DrGlaucous/UFBTM/Media/flipped.jpg

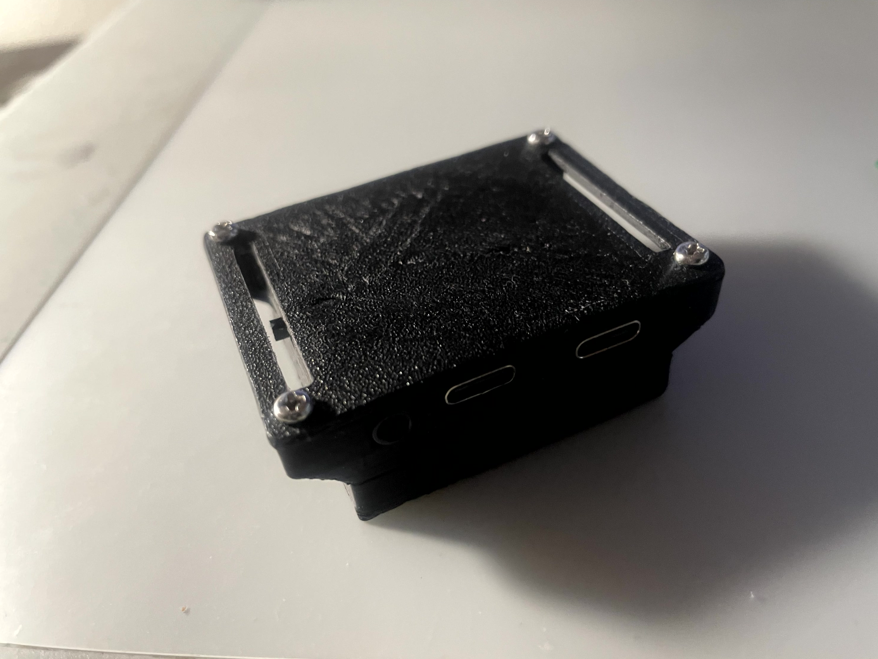
Media/flipped.jpg
