DrGlaucous/UFBTM/Media/upright.jpg

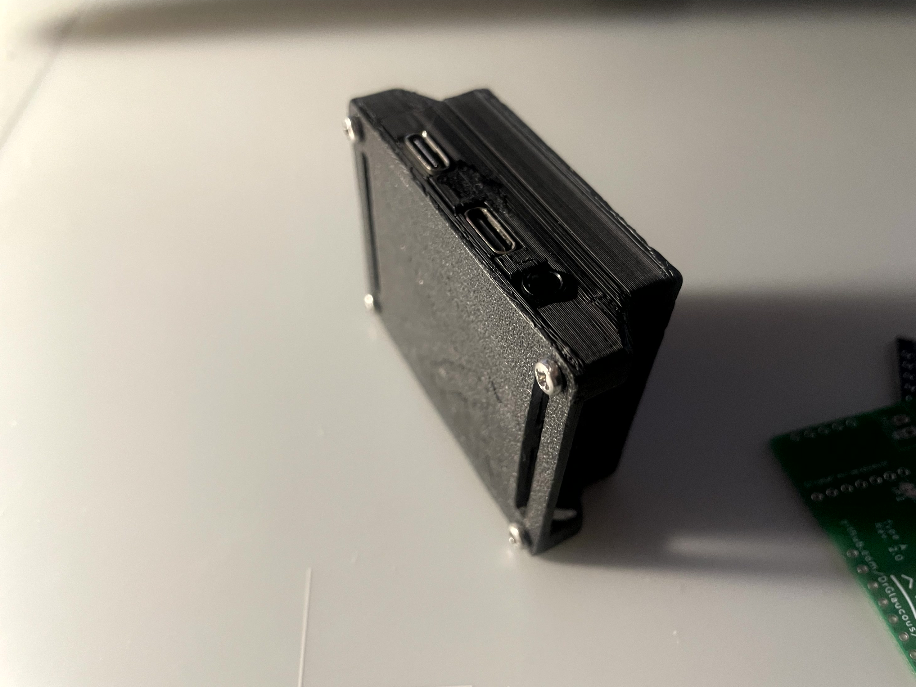
Media/upright.jpg
