DrGlaucous/UFBTM/Reference/LX-LBC3 - TP4057.jpg

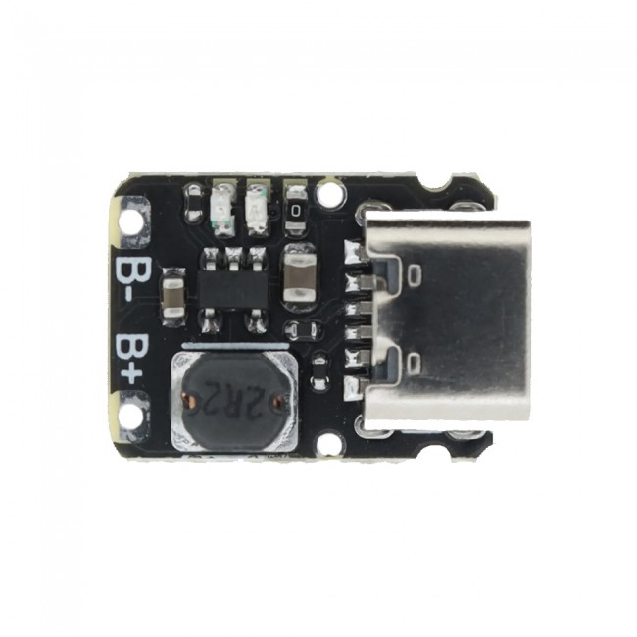
Reference/LX-LBC3 - TP4057.jpg
