DrGlaucous/UFBTM/Reference/LX-LBC3.png

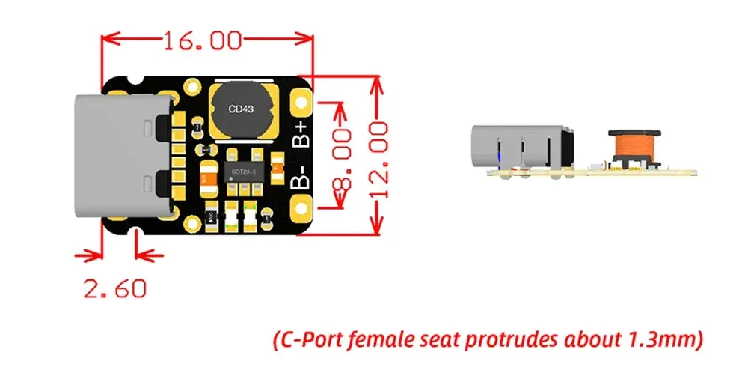
Reference/LX-LBC3.png
