DrGlaucous/UFBTM/Reference/SS12D06.jpg

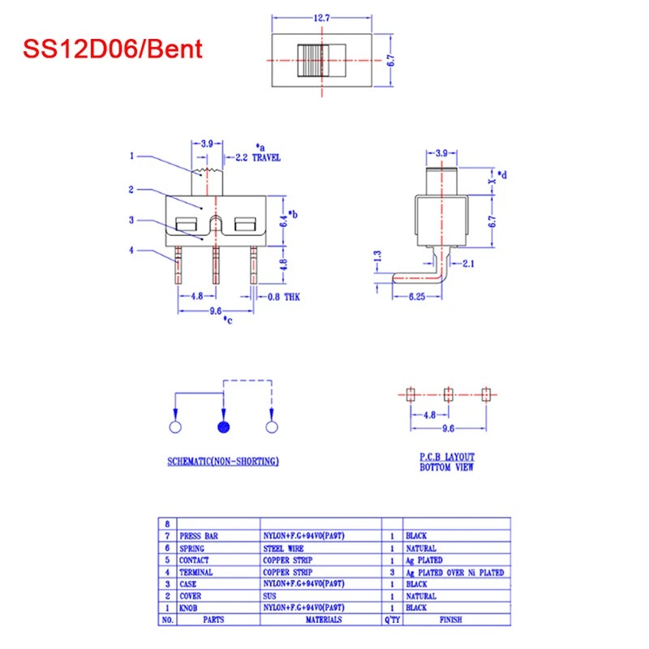
Reference/SS12D06.jpg
