DrGlaucous/UFBTM/Reference/SS12D10.jpg

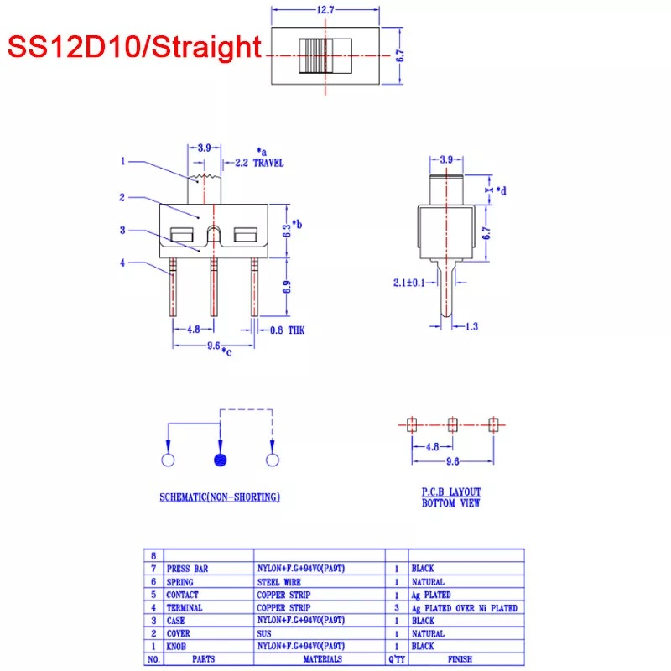
Reference/SS12D10.jpg
