DrGlaucous/UFBTM/Reference/SS12F21.jpg

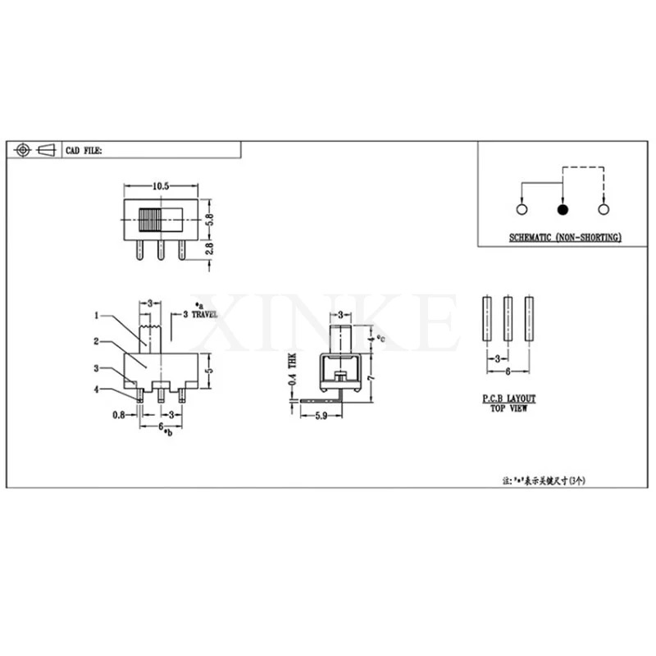
Reference/SS12F21.jpg
