DrGlaucous/UFBTM/Reference/TP4057-1A-TIPO-C.jpg

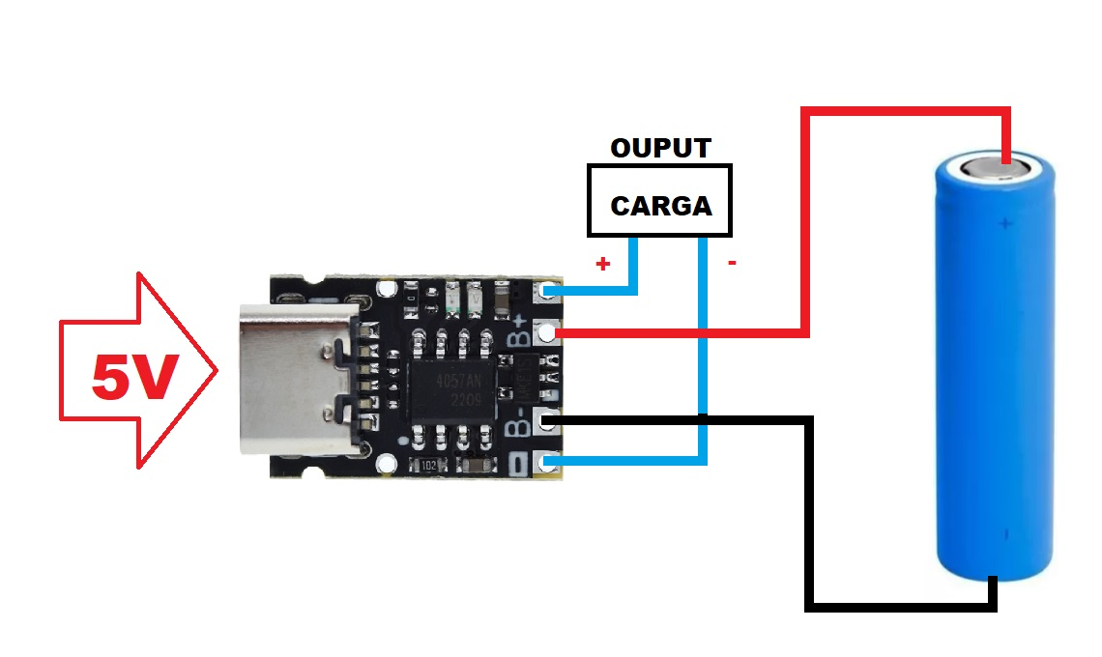
Reference/TP4057-1A-TIPO-C.jpg
