DrGlaucous/UFBTM/Firmware/SlimeVR-Tracker-ESP-0.5.2/src/defines_bmi160.h

/*
	SlimeVR Code is placed under the MIT license
	Copyright (c) 2022 SlimeVR Contributors

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
	THE SOFTWARE IS PROVIDED "AS IS", WITHOUT WARRANTY OF ANY KIND, EXPRESS OR
	IMPLIED, INCLUDING BUT NOT LIMITED TO THE WARRANTIES OF MERCHANTABILITY,
	FITNESS FOR A PARTICULAR PURPOSE AND NONINFRINGEMENT. IN NO EVENT SHALL THE
	AUTHORS OR COPYRIGHT HOLDERS BE LIABLE FOR ANY CLAIM, DAMAGES OR OTHER
	LIABILITY, WHETHER IN AN ACTION OF CONTRACT, TORT OR OTHERWISE, ARISING FROM,
	OUT OF OR IN CONNECTION WITH THE SOFTWARE OR THE USE OR OTHER DEALINGS IN
	THE SOFTWARE.
*/
#ifndef BMI160_DEFINES_H
#define BMI160_DEFINES_H

// BMI160 magnetometer type, applies to both main and aux trackers, mixed types are not
// supported currently. If only 1 out of 2 trackers has a mag, the tracker without a mag
// note: this now also applies to the LSM6DS3 IMU, with potential for other IMUs to work with it as well. (but I don't have those to test with)
// should still function normally. NOT USED if USE_6_AXIS == true. Pick one:
// #define BMI160_MAG_TYPE BMI160_MAG_TYPE_HMC
// #define BMI160_MAG_TYPE BMI160_MAG_TYPE_QMC
#define BMI160_MAG_TYPE BMI160_MAG_TYPE_QMP

//unused (both of these settings have been moved to SENSOR_USE_XXX)
// Use VQF instead of mahony sensor fusion.
// Features: rest bias estimation, magnetic distortion rejection.
// #define BMI160_USE_VQF true

//unused
// Use BasicVQF instead of VQF (if BMI160_USE_VQF == true).
// Disables the features above.
//#define BMI160_USE_BASIC_VQF false


// Use temperature calibration.
#define BMI160_USE_TEMPCAL true

// How long to run gyro calibration for.
// Disables this calibration step if value is 0.
// Default: 5
#define BMI160_CALIBRATION_GYRO_SECONDS 5

// Calibration method options:
// - Skip: disable this calibration step;
// - Rotation: rotate the device in hand;
// - 6 point: put the device in 6 unique orientations.
// Default: ACCEL_CALIBRATION_METHOD_6POINT
// #define BMI160_ACCEL_CALIBRATION_METHOD ACCEL_CALIBRATION_METHOD_SKIP
// #define BMI160_ACCEL_CALIBRATION_METHOD ACCEL_CALIBRATION_METHOD_ROTATION
#define BMI160_ACCEL_CALIBRATION_METHOD ACCEL_CALIBRATION_METHOD_6POINT

// How long to run magnetometer calibration for, if enabled and you have added a
// magnetometer. Magnetometer will not be used until you calibrate it. Disables this
// calibration step if value is 0. NOT USED if USE_6_AXIS == true Default: 20
#define BMI160_CALIBRATION_MAG_SECONDS 20

// Send temperature to the server as AXXYY,
// where XX is calibration progress from 0 to 60, and YY is temperature,
// A is 1: not in calibration mode or 2: calibration in progress.
#define BMI160_TEMPCAL_DEBUG false

// Print debug info every second.
#define BMI160_DEBUG true

// Use sensitivity calibration.
#define BMI160_USE_SENSCAL true

#endif
