DrGlaucous/UFBTM/Firmware/SlimeVR-Tracker-ESP-0.5.2/src/sensors/sensor.h

/*
	SlimeVR Code is placed under the MIT license
	Copyright (c) 2021 Eiren Rain & SlimeVR contributors

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
	THE SOFTWARE IS PROVIDED "AS IS", WITHOUT WARRANTY OF ANY KIND, EXPRESS OR
	IMPLIED, INCLUDING BUT NOT LIMITED TO THE WARRANTIES OF MERCHANTABILITY,
	FITNESS FOR A PARTICULAR PURPOSE AND NONINFRINGEMENT. IN NO EVENT SHALL THE
	AUTHORS OR COPYRIGHT HOLDERS BE LIABLE FOR ANY CLAIM, DAMAGES OR OTHER
	LIABILITY, WHETHER IN AN ACTION OF CONTRACT, TORT OR OTHERWISE, ARISING FROM,
	OUT OF OR IN CONNECTION WITH THE SOFTWARE OR THE USE OR OTHER DEALINGS IN
	THE SOFTWARE.
*/

#ifndef SLIMEVR_SENSOR_H_
#define SLIMEVR_SENSOR_H_

#include <Arduino.h>
#include <quat.h>
#include <vector3.h>

#include "configuration/Configuration.h"
#include "globals.h"
#include "logging/Logger.h"
#include "utils.h"

#define DATA_TYPE_NORMAL 1
#define DATA_TYPE_CORRECTION 2

enum class SensorStatus : uint8_t {
	SENSOR_OFFLINE = 0,
	SENSOR_OK = 1,
	SENSOR_ERROR = 2
};

enum class MagnetometerStatus : uint8_t {
	MAG_NOT_SUPPORTED = 0,
	MAG_DISABLED = 1,
	MAG_ENABLED = 2,
};

class Sensor {
public:
	Sensor(
		const char* sensorName,
		ImuID type,
		uint8_t id,
		uint8_t address,
		float rotation,
		uint8_t sclpin = 0,
		uint8_t sdapin = 0
	)
		: addr(address)
		, sensorId(id)
		, sensorType(type)
		, sensorOffset({Quat(Vector3(0, 0, 1), rotation)})
		, m_Logger(SlimeVR::Logging::Logger(sensorName))
		, sclPin(sclpin)
		, sdaPin(sdapin) {
		char buf[4];
		sprintf(buf, "%u", id);
		m_Logger.setTag(buf);
	}

	virtual ~Sensor(){};
	virtual void motionSetup(){}; //all
	virtual void postSetup(){}; //BNO080
	virtual void motionLoop(){}; //all
	virtual void sendData(); //BNO080
	virtual void setAcceleration(Vector3 a); //all
	virtual void setFusedRotation(Quat r); //all
	virtual void startCalibration(int calibrationType){}; //all
	virtual SensorStatus getSensorState(); //bmi + error sensors
	virtual void printTemperatureCalibrationState(); //bmi160
	virtual void printDebugTemperatureCalibrationState(); //bmi160
	virtual void resetTemperatureCalibrationState(); //bmi160
	virtual void saveTemperatureCalibration(); //all
	virtual void setFlag(uint16_t flagId, bool state){}; //mainly for BNO080
	virtual uint16_t getSensorConfigData(); //defined in sensor.cpp
	bool isWorking() { return working; };
	bool getHadData() const { return hadData; };
	bool isValid() { return sclPin != sdaPin; };
	bool isMagEnabled() { return magStatus == MagnetometerStatus::MAG_ENABLED; };
	uint8_t getSensorId() { return sensorId; };
	ImuID getSensorType() { return sensorType; };
	MagnetometerStatus getMagStatus() { return magStatus; };
	const Vector3& getAcceleration() { return acceleration; };
	const Quat& getFusedRotation() { return fusedRotation; };
	bool hasNewDataToSend() { return newFusedRotation || newAcceleration; };

protected:
	uint8_t addr = 0;
	uint8_t sensorId = 0;
	ImuID sensorType = ImuID::Unknown;
	bool working = false;
	bool hadData = false;
	uint8_t calibrationAccuracy = 0;
	MagnetometerStatus magStatus = MagnetometerStatus::MAG_NOT_SUPPORTED;
	Quat sensorOffset;

	bool newFusedRotation = false;
	Quat fusedRotation{};
	Quat lastFusedRotationSent{};

	bool newAcceleration = false;
	Vector3 acceleration{};

	mutable SlimeVR::Logging::Logger m_Logger;

public:
	uint8_t sclPin = 0;
	uint8_t sdaPin = 0;

private:
	void printTemperatureCalibrationUnsupported();
};

const char* getIMUNameByType(ImuID imuType);

#endif  // SLIMEVR_SENSOR_H_
