DrGlaucous/UFBTM/Firmware/0.5.2_Flip_Backup/src/sensors/mpu9250sensor.h

/*
	SlimeVR Code is placed under the MIT license
	Copyright (c) 2021 Eiren Rain & SlimeVR contributors

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
	THE SOFTWARE IS PROVIDED "AS IS", WITHOUT WARRANTY OF ANY KIND, EXPRESS OR
	IMPLIED, INCLUDING BUT NOT LIMITED TO THE WARRANTIES OF MERCHANTABILITY,
	FITNESS FOR A PARTICULAR PURPOSE AND NONINFRINGEMENT. IN NO EVENT SHALL THE
	AUTHORS OR COPYRIGHT HOLDERS BE LIABLE FOR ANY CLAIM, DAMAGES OR OTHER
	LIABILITY, WHETHER IN AN ACTION OF CONTRACT, TORT OR OTHERWISE, ARISING FROM,
	OUT OF OR IN CONNECTION WITH THE SOFTWARE OR THE USE OR OTHER DEALINGS IN
	THE SOFTWARE.
*/

#ifndef SENSORS_MPU9250SENSOR_H
#define SENSORS_MPU9250SENSOR_H

#include <MPU9250_6Axis_MotionApps_V6_12.h>

#include "logging/Logger.h"
#include "sensor.h"

#define MPU9250_DEFAULT_ODR_HZ 8000.0f
#define MPU9250_SAMPLE_DIV 39
constexpr float MPU9250_ODR_TS
	= (1.0f / MPU9250_DEFAULT_ODR_HZ) * (1 + MPU9250_SAMPLE_DIV);

#define MPU_USE_DMPMAG 1

#if MPU_USE_DMPMAG
#include "SensorFusionDMP.h"
#else
#include "SensorFusion.h"
#endif

class MPU9250Sensor : public Sensor {
public:
	static constexpr auto TypeID = ImuID::MPU9250;
	static constexpr uint8_t Address = 0x68;

	MPU9250Sensor(
		uint8_t id,
		uint8_t addrSuppl,
		float rotation,
		bool flip,
		uint8_t sclPin,
		uint8_t sdaPin,
		uint8_t
	)
		: Sensor(
			"MPU9250Sensor",
			ImuID::MPU9250,
			id,
			Address + addrSuppl,
			rotation,
			flip,
			sclPin,
			sdaPin
		)
#if !MPU_USE_DMPMAG
		, sfusion(MPU9250_ODR_TS)
#endif
			  {};
	~MPU9250Sensor(){};
	void motionSetup() override final;
	void motionLoop() override final;
	void startCalibration(int calibrationType) override final;
	void getMPUScaled();

private:
	MPU9250 imu{};
	bool dmpReady = false;  // set true if DMP init was successful
	// TODO: actually check interrupt status
	// uint8_t mpuIntStatus;     // holds actual interrupt status byte from MPU
	uint16_t packetSize;  // expected DMP packet size (default is 42 bytes)

#if MPU_USE_DMPMAG
	SlimeVR::Sensors::SensorFusionDMP sfusion;
#else
	SlimeVR::Sensors::SensorFusion sfusion;
#endif

	// raw data and scaled as vector
	float Axyz[3]{};
	float Gxyz[3]{};
	float Mxyz[3]{};
	VectorInt16 rawAccel{};
	Quat correction{0, 0, 0, 0};

	SlimeVR::Configuration::MPU9250SensorConfig m_Config = {};

	// outputs to respective member variables
	void parseAccelData(int16_t data[3]);
	void parseGyroData(int16_t data[3]);
	void parseMagData(int16_t data[3]);

	// 6 bytes for gyro, 6 bytes for accel, 7 bytes for magnetometer
	static constexpr uint16_t sensor_data_len = 19;

	struct fifo_sample {
		int16_t accel[3];
		int16_t gyro[3];
		int16_t mag[3];
		uint8_t mag_status;
	};

	// acts as a memory space for getNextSample. upon success, can read from the sample
	// member
	// TODO: this may be overcomplicated, we may be able to just use fifo_sample and i
	// misunderstood strict aliasing rules.
	union fifo_sample_raw {
		uint8_t raw[sensor_data_len];
		struct fifo_sample sample;
	};

	// returns true if sample was read, outputs number of waiting samples in
	// remaining_count if not null.
	bool getNextSample(union fifo_sample_raw* buffer, uint16_t* remaining_count);
	static void swapFifoData(union fifo_sample_raw* sample);
};

#endif
